algofoogle/tt07-raybox-zero/test/tb.v

`default_nettype none
`timescale 1ns / 1ps

/* This testbench just instantiates the module and makes some convenient wires
   that can be driven / tested by the cocotb test.py.
*/

// `define DUMP_VCD

module tb ();

  //NOTE: DON'T write VCD file, because it'd be huge!
  // // Dump the signals to a VCD file. You can view it with gtkwave.
`ifdef DUMP_VCD
  initial begin
    $dumpfile("tb.vcd");
    $dumpvars(0, tb);
    #1;
  end
`endif

  // --- Named inputs controlled by test: ---
  // Universal TT07 inputs:
  reg clk;
  reg rst_n;
  reg ena;
  // Specific inputs for raybox-zero:
  reg pov_sclk;
  reg pov_mosi;
  reg pov_ss_n;
  reg debug;
  reg inc_px;
  reg inc_py;
  reg registered_outputs; // aka just 'reg'
  reg gen_tex;
  reg reg_sclk;
  reg reg_mosi;
  reg reg_ss_n;
  // Specific outputs for raybox-zero:
  // RrGgBb and H/Vsync pin ordering is per Tiny VGA PMOD
  // (https://tinytapeout.com/specs/pinouts/#vga-output)
  wire [1:0] rr = {uo_out[0],uo_out[4]};
  wire [1:0] gg = {uo_out[1],uo_out[5]};
  wire [1:0] bb = {uo_out[2],uo_out[6]};
  wire [5:0] rgb = {rr,gg,bb}; // Just used by cocotb test bench for convenient checks.
  wire hsync_n    = uo_out[7];
  wire vsync_n    = uo_out[3];
  //wire o_hblank   = uio_out[0];
  //wire o_vblank   = uio_out[1];
  wire tex_csb    = uio_out[0];
  wire tex_sclk   = uio_out[1];

  // --- DUT's generic IOs from the TT wrapper ---
  wire [7:0] ui_in;       // Dedicated inputs
  wire [7:0] uo_out;      // Dedicated outputs
  wire [7:0] uio_in;      // Bidir IOs: Input path
  wire [7:0] uio_out;     // Bidir IOs: Output path
  wire [7:0] uio_oe;      // Bidir IOs: Enable path (active high: 0=input, 1=output).

  assign ui_in = {
    gen_tex,
    registered_outputs,
    inc_py,
    inc_px,
    debug,
    pov_ss_n,
    pov_mosi,
    pov_sclk
  };

  assign uio_in = {
    tex_io, // [2:0]
    reg_ss_n,
    reg_mosi,
    reg_sclk,
    2'b00 // Unused (outputs only).
  };

  wire [2:0] tex_io;

  assign tex_io[0] =
    (uio_oe[5] == 1)  ? uio_out[5]  // raybox-zero is asserting an output.
                      : 1'bz;       // raybox-zero is reading (or not using).

  tt_um_algofoogle_raybox_zero user_project (

      // Include power ports for the Gate Level test:
`ifdef GL_TEST
      .VPWR(1'b1),
      .VGND(1'b0),
`endif

      .ui_in  (ui_in),    // Dedicated inputs
      .uo_out (uo_out),   // Dedicated outputs
      .uio_in (uio_in),   // IOs: Input path
      .uio_out(uio_out),  // IOs: Output path
      .uio_oe (uio_oe),   // IOs: Enable path (active high: 0=input, 1=output)
      .ena    (ena),      // enable - goes high when design is selected
      .clk    (clk),      // clock
      .rst_n  (rst_n)     // not reset
  );

  // Connect our relevant TT pins to our texture SPI flash ROM:
  W25Q128JVxIM texture_rom(
      .DIO    (tex_io[0]),    // SPI io0 (MOSI) - BIDIRECTIONAL
      .DO     (tex_io[1]),    // SPI io1 (MISO)
      .WPn    (tex_io[2]),    // SPI io2
      //.HOLDn  (1'b1),       // SPI io3. //NOTE: Not used in raybox-zero.
      .CSn    (uio_out[0]),   // SPI /CS
      .CLK    (uio_out[1])    // SPI SCLK
  );


endmodule
